MihaiCatalin-Stan/ebook-reader-pcb-design/Images/Display.png

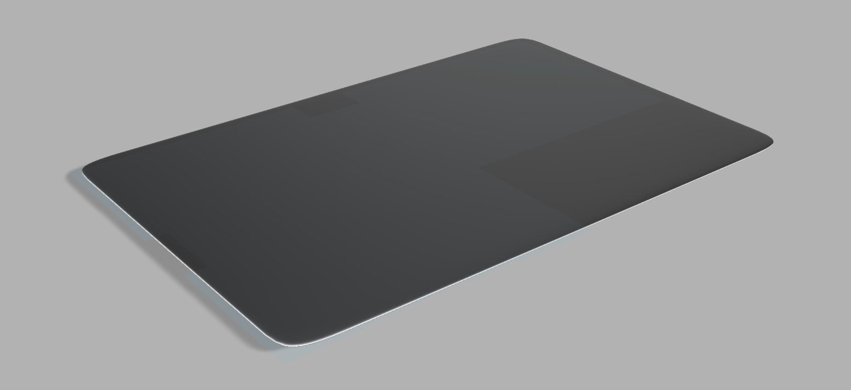
Images/Display.png
