MihaiCatalin-Stan/ebook-reader-pcb-design/Images/PCB Bottom Layer.png

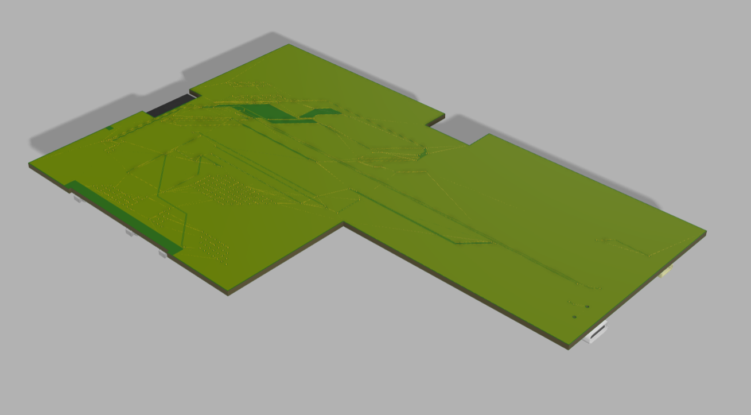
Images/PCB Bottom Layer.png
